qishengen/AIMonitor/scr/1.png

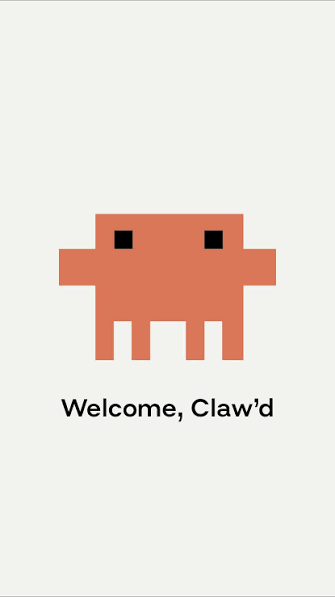
scr/1.png
