qishengen/AIMonitor/Code/AIMonitor/idle_anim.h

#pragma once
#include <stdint.h>

#define IDLE_ANIM_W 64
#define IDLE_ANIM_H 64
#define IDLE_ANIM_FRAME_COUNT 2

// 设备显示为 LSB 位序：字节 bit0 = 最左像素
const unsigned char idle_anim[IDLE_ANIM_FRAME_COUNT][IDLE_ANIM_W * IDLE_ANIM_H / 8] = {
  {  // frame 0: 外框
    0x00, 0x00, 0x00, 0x00, 0x00, 0x00, 0x00, 0x00,
    0x00, 0x00, 0x00, 0x00, 0x00, 0x00, 0x00, 0x00,
    0x00, 0x00, 0x00, 0x00, 0x00, 0x00, 0x00, 0x00,
    0x00, 0x00, 0x00, 0x00, 0x00, 0x00, 0x00, 0x00,
    0x00, 0x00, 0x00, 0x00, 0x00, 0x00, 0x00, 0x00,
    0x00, 0x00, 0x00, 0x00, 0x00, 0x00, 0x00, 0x00,
    0x00, 0x00, 0x00, 0x00, 0x00, 0x00, 0x00, 0x00,
    0x00, 0x00, 0x00, 0x00, 0x00, 0x00, 0x00, 0x00,
    0x00, 0x00, 0x00, 0x00, 0x00, 0x00, 0x00, 0x00,
    0x00, 0x00, 0x00, 0x00, 0x00, 0x00, 0x00, 0x00,
    0x00, 0x00, 0x00, 0x00, 0x00, 0x00, 0x00, 0x00,
    0x00, 0x00, 0x00, 0x00, 0x00, 0x00, 0x00, 0x00,
    0x00, 0x00, 0x00, 0x00, 0x00, 0x00, 0x00, 0x00,
    0x00, 0x00, 0x00, 0x00, 0x00, 0x00, 0x00, 0x00,
    0x00, 0x00, 0x00, 0x00, 0x00, 0x00, 0x00, 0x00,
    0x00, 0x00, 0x00, 0x00, 0x00, 0x00, 0x00, 0x00,
    0x00, 0x00, 0x00, 0x00, 0x00, 0x00, 0x00, 0x00,
    0x00, 0x00, 0x00, 0x00, 0x00, 0x00, 0x00, 0x00,
    0x00, 0x00, 0x00, 0x00, 0x00, 0x00, 0x00, 0x00,
    0x00, 0x00, 0x00, 0x00, 0x00, 0x00, 0x00, 0x00,
    0x00, 0x00, 0xF0, 0xFF, 0xFF, 0x0F, 0x00, 0x00,
    0x00, 0x00, 0x10, 0x00, 0x00, 0x08, 0x00, 0x00,
    0x00, 0x00, 0x10, 0x00, 0x00, 0x08, 0x00, 0x00,
    0x00, 0x00, 0x10, 0x00, 0x00, 0x08, 0x00, 0x00,
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
    0x00, 0x00, 0xF0, 0xFF, 0xFF, 0x0F, 0x00, 0x00,
    0x00, 0x00, 0xF0, 0xFF, 0xFF, 0x0F, 0x00, 0x00,
    0x00, 0x00, 0xF0, 0xFF, 0xFF, 0x0F, 0x00, 0x00,
    0x00, 0x00, 0xF0, 0xFF, 0xFF, 0x0F, 0x00, 0x00,
    0x00, 0x00, 0xF0, 0xFF, 0xFF, 0x0F, 0x00, 0x00,
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
  }
};
